Pricey1600/TVOC-eCO2-Sensor/Images/diy_tvoc_sensor.jpg

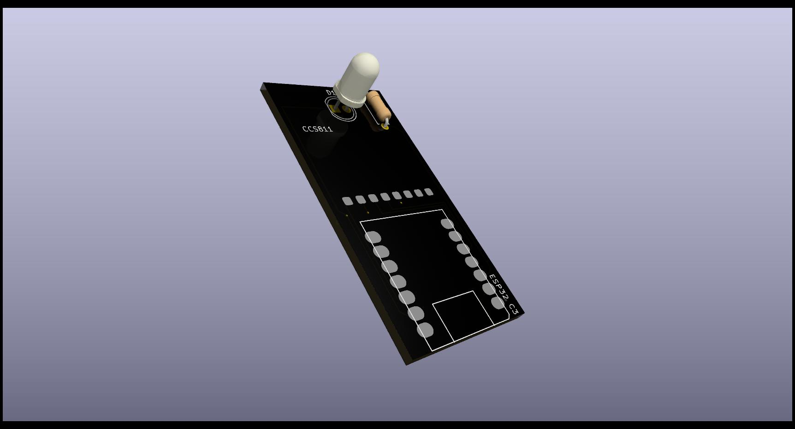
Images/diy_tvoc_sensor.jpg
