Pricey1600/TVOC-eCO2-Sensor/Images/TVOC sesnor final (2).jpg

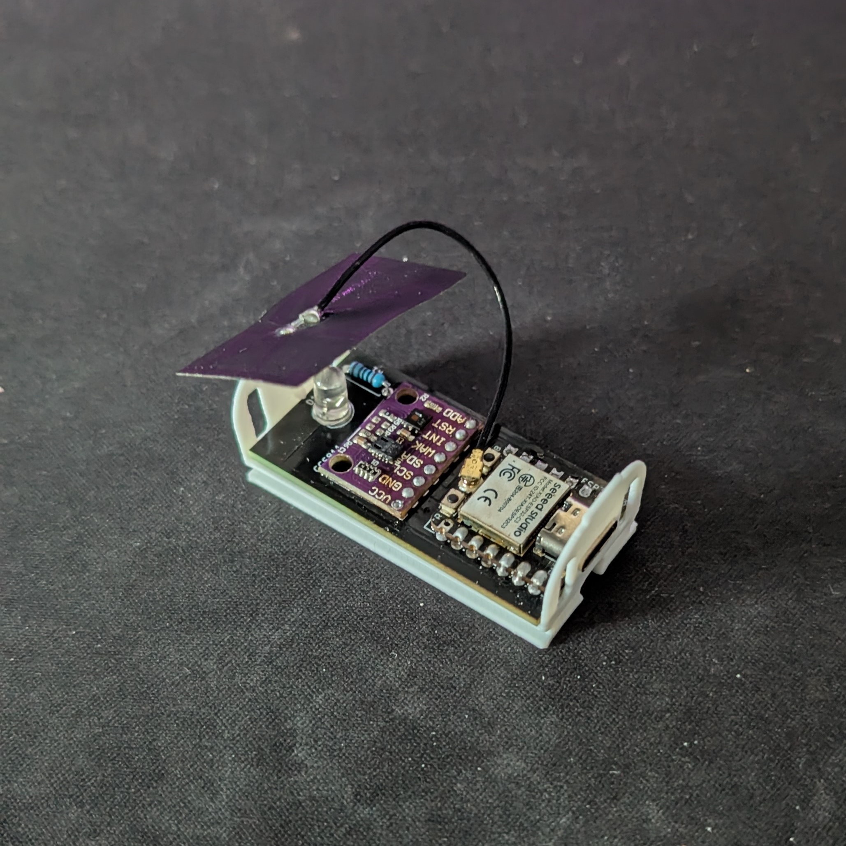
Images/TVOC sesnor final (2).jpg
